alllhappy/K-Map-Calculator/report/assets/calc.png

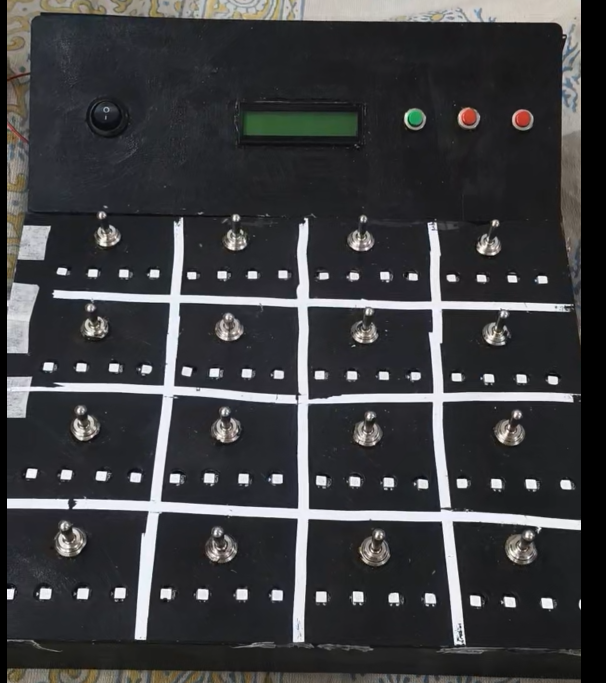
report/assets/calc.png
