alllhappy/K-Map-Calculator/schematic/Kmap_ckt.kicad_sch

## KiCad design schematic/Kmap_ckt.kicad_sch (2026-09-30)

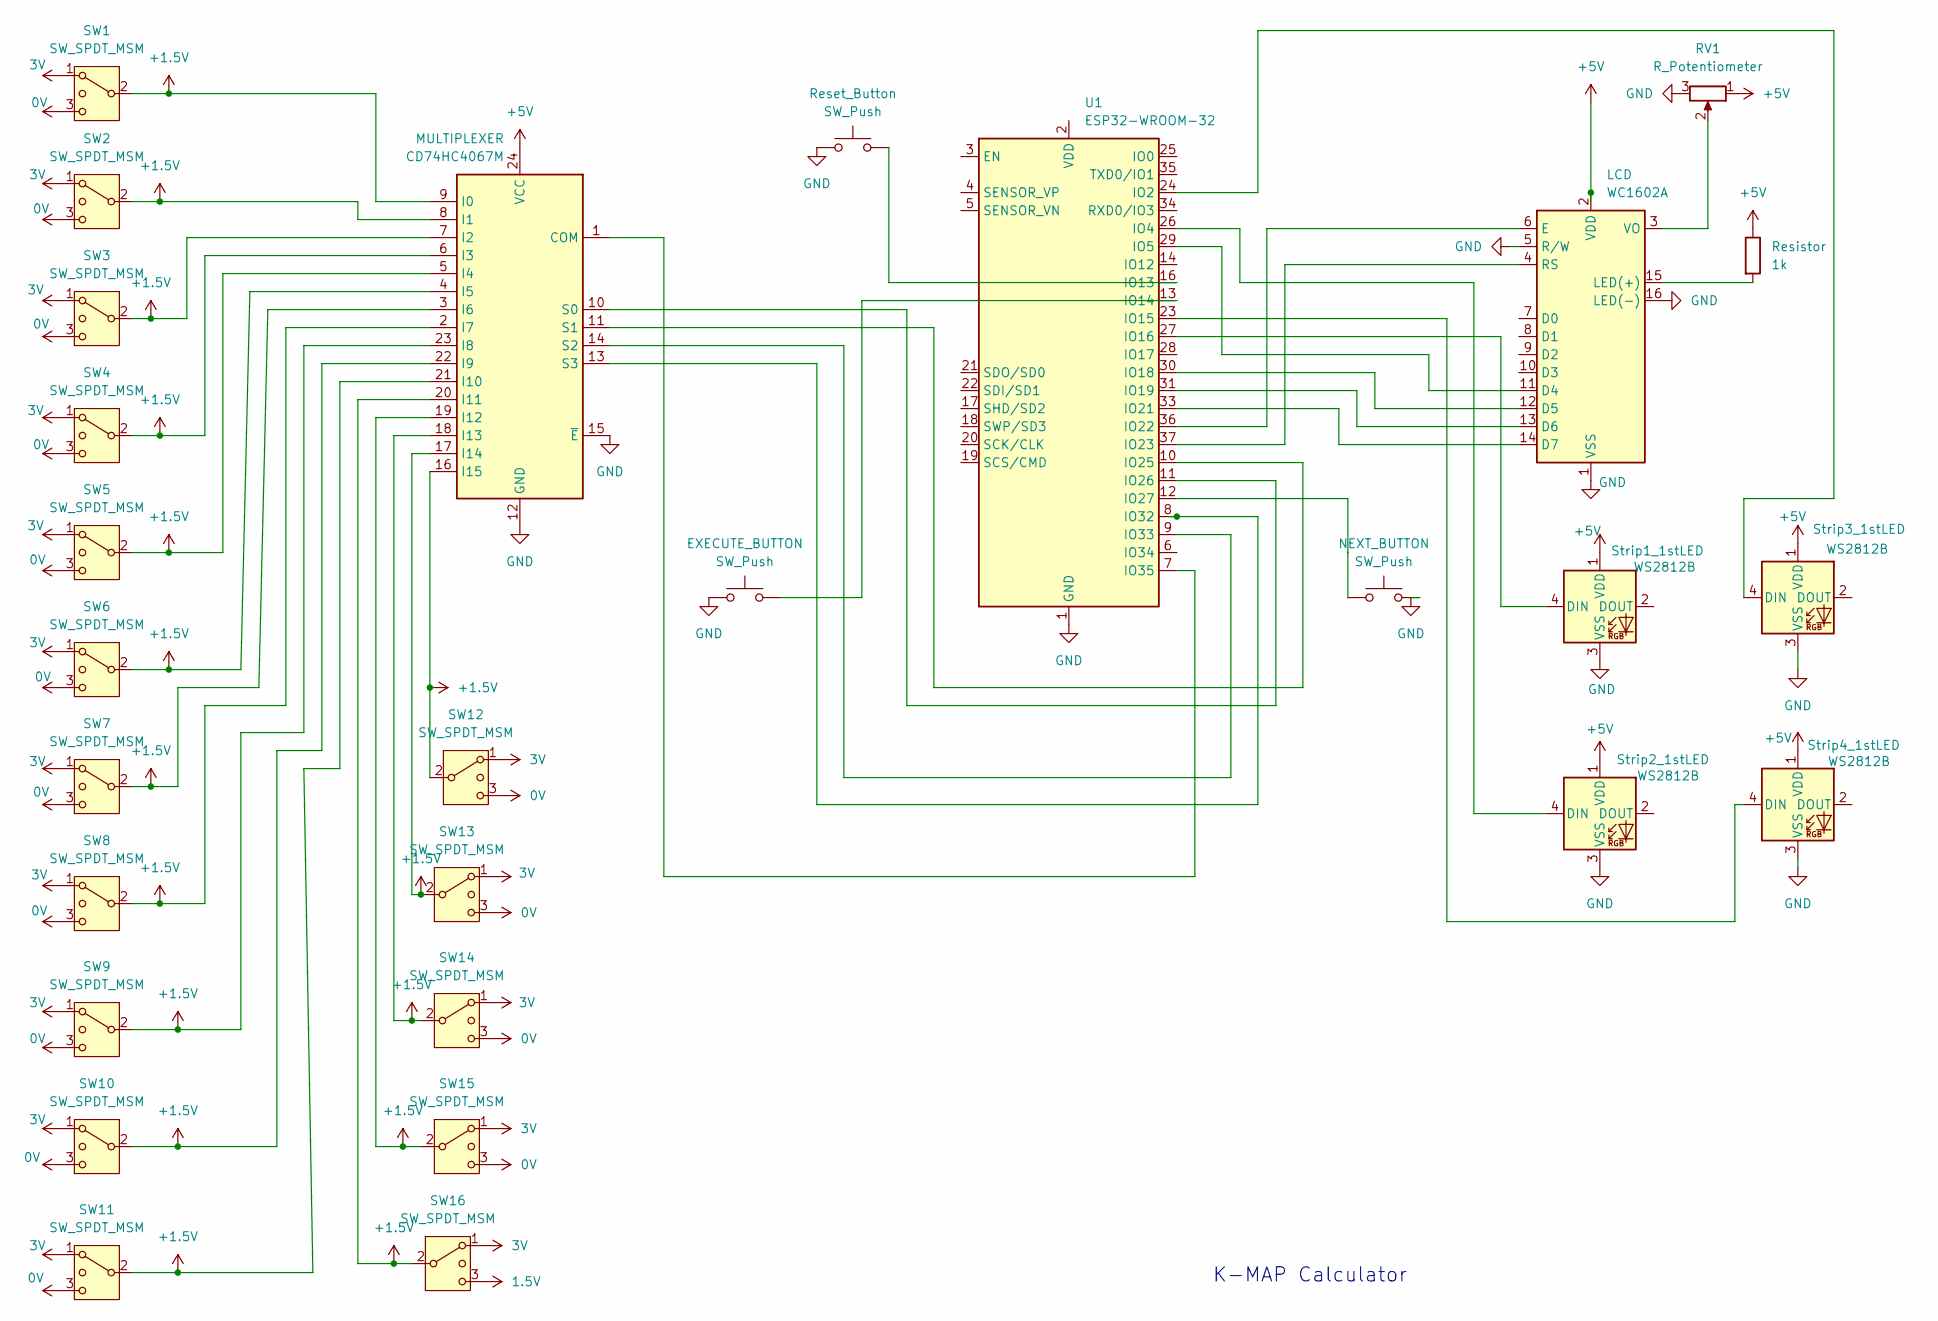
[picture p44: schematic Kmap_ckt.kicad_sch]

Parts:
EXECUTE_BUTTON: SW_Push
LCD: WC1602A
MULTIPLEXER: CD74HC4067M; SOIC-24W_7.5x15.4mm_P1.27mm
NEXT_BUTTON: SW_Push
RV1: R_Potentiometer
Reset_Button: SW_Push
Resistor: 1k
SW1, SW2, SW3, SW4, SW5, SW6, SW7, SW8, SW9, SW10, SW11, SW12, SW13, SW14, SW15, SW16: SW_SPDT_MSM
Strip1_1stLED, Strip2_1stLED, Strip3_1stLED, Strip4_1stLED: WS2812B; LED_WS2812B_PLCC4_5.0x5.0mm_P3.2mm
U1: ESP32-WROOM-32

Connections:
0V: SW1.3 (4), SW2.3 (4), SW3.3 (4), SW4.3 (4), SW5.3 (4), SW6.3 (4), SW7.3 (4), SW8.3 (4), SW9.3 (4), SW10.3 (4), SW11.3 (4), SW12.3 (4), SW13.3 (4), SW14.3 (4), SW15.3 (4)
1.5V: SW16.3 (4)
3V: SW1.1, SW2.1, SW3.1, SW4.1, SW5.1, SW6.1, SW7.1, SW8.1, SW9.1, SW10.1, SW11.1, SW12.1, SW13.1, SW14.1, SW15.1, SW16.1
+1.5V: MULTIPLEXER.2 (I7), MULTIPLEXER.3 (I6), MULTIPLEXER.4 (I5), MULTIPLEXER.5 (I4), MULTIPLEXER.6 (I3), MULTIPLEXER.7 (I2), MULTIPLEXER.8 (I1), MULTIPLEXER.9 (I0), MULTIPLEXER.16 (I15), MULTIPLEXER.17 (I14), MULTIPLEXER.18 (I13), MULTIPLEXER.19 (I12), MULTIPLEXER.20 (I11), MULTIPLEXER.21 (I10), MULTIPLEXER.22 (I9), MULTIPLEXER.23 (I8), SW1.2 (3), SW2.2 (3), SW3.2 (3), SW4.2 (3), SW5.2 (3), SW6.2 (3), SW7.2 (3), SW8.2 (3), SW9.2 (3), SW10.2 (3), SW11.2 (3), SW12.2 (3), SW13.2 (3), SW14.2 (3), SW15.2 (3), SW16.2 (3)
+5V: LCD.2 (VDD), MULTIPLEXER.24 (VCC), RV1.1, Resistor.1, Strip1_1stLED.1 (VDD), Strip2_1stLED.1 (VDD), Strip3_1stLED.1 (VDD), Strip4_1stLED.1 (VDD)
GND: EXECUTE_BUTTON.1, LCD.1 (VSS), LCD.5 (R/W), LCD.16 (LED(-)), MULTIPLEXER.12 (GND), MULTIPLEXER.15 (~E), NEXT_BUTTON.2, RV1.3, Reset_Button.1, Strip1_1stLED.3 (VSS), Strip2_1stLED.3 (VSS), Strip3_1stLED.3 (VSS), Strip4_1stLED.3 (VSS), U1.1 (GND), U1.15 (GND), U1.38 (GND), U1.39 (GND)
unnamed: EXECUTE_BUTTON.2, U1.13 (IO14)
unnamed: LCD.3 (VO), RV1.2
unnamed: LCD.4 (RS), U1.37 (IO23)
unnamed: LCD.6 (E), U1.36 (IO22)
unnamed: LCD.11 (D4), U1.29 (IO5)
unnamed: LCD.12 (D5), U1.30 (IO18)
unnamed: LCD.13 (D6), U1.31 (IO19)
unnamed: LCD.14 (D7), U1.33 (IO21)
unnamed: LCD.15 (LED(+)), Resistor.2
unnamed: MULTIPLEXER.1 (COM), U1.7 (IO35)
unnamed: MULTIPLEXER.10 (S0), U1.11 (IO26)
unnamed: MULTIPLEXER.11 (S1), U1.10 (IO25)
unnamed: MULTIPLEXER.13 (S3), U1.8 (IO32)
unnamed: MULTIPLEXER.14 (S2), U1.9 (IO33)
unnamed: NEXT_BUTTON.1, U1.12 (IO27)
unnamed: Reset_Button.2, U1.16 (IO13)
unnamed: Strip1_1stLED.4 (DIN), U1.27 (IO16)
unnamed: Strip2_1stLED.4 (DIN), U1.26 (IO4)
unnamed: Strip3_1stLED.4 (DIN), U1.24 (IO2)
unnamed: Strip4_1stLED.4 (DIN), U1.23 (IO15)

Notes on the sheet:
K-MAP Calculator
